I-AM-ENGINEER/AudMX/Images/photo_2024-06-28_22-19-17.jpg

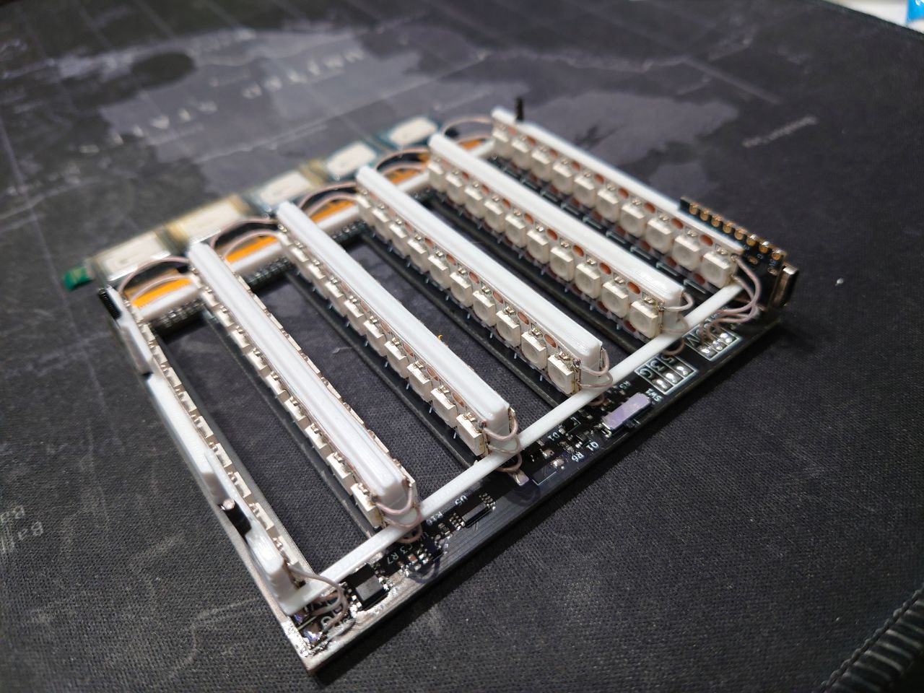
Images/photo_2024-06-28_22-19-17.jpg
