I-AM-ENGINEER/AudMX/AudMix/include/AudMX_logo.h

#pragma once

// 'A', 60x44px
const unsigned char epd_bitmap_A [] = {
	0x00, 0x00, 0x00, 0x7f, 0xe0, 0x00, 0x00, 0x00, 0x00, 0x00, 0x00, 0xff, 0xf0, 0x00, 0x00, 0x00, 
	0x00, 0x00, 0x00, 0xff, 0xf0, 0x00, 0x00, 0x00, 0x00, 0x00, 0x00, 0xff, 0xf0, 0x00, 0x00, 0x00, 
	0x00, 0x00, 0x01, 0xff, 0xf8, 0x00, 0x00, 0x00, 0x00, 0x00, 0x01, 0xff, 0xf8, 0x00, 0x00, 0x00, 
	0x00, 0x00, 0x03, 0xff, 0xf8, 0x00, 0x00, 0x00, 0x00, 0x00, 0x03, 0xff, 0xfc, 0x00, 0x00, 0x00, 
	0x00, 0x00, 0x03, 0xff, 0xfc, 0x00, 0x00, 0x00, 0x00, 0x00, 0x07, 0xff, 0xfc, 0x00, 0x00, 0x00, 
	0x00, 0x00, 0x07, 0xff, 0xfe, 0x00, 0x00, 0x00, 0x00, 0x00, 0x07, 0xfb, 0xfe, 0x00, 0x00, 0x00, 
	0x00, 0x00, 0x0f, 0xf9, 0xfe, 0x00, 0x00, 0x00, 0x00, 0x00, 0x0f, 0xf9, 0xff, 0x00, 0x00, 0x00, 
	0x00, 0x00, 0x0f, 0xf1, 0xff, 0x00, 0x00, 0x00, 0x00, 0x00, 0x1f, 0xf0, 0xff, 0x80, 0x00, 0x00, 
	0x00, 0x00, 0x1f, 0xf0, 0xff, 0x80, 0x00, 0x00, 0x00, 0x00, 0x1f, 0xe0, 0xff, 0x80, 0x00, 0x00, 
	0x00, 0x00, 0x3f, 0xe0, 0x7f, 0xc0, 0x00, 0x00, 0x00, 0x00, 0x3f, 0xe0, 0x7f, 0xc0, 0x00, 0x00, 
	0x00, 0x00, 0x7f, 0xc0, 0x7f, 0xc0, 0x00, 0x00, 0x00, 0x00, 0x7f, 0xc0, 0x3f, 0xe0, 0x00, 0x00, 
	0x00, 0x00, 0x7f, 0xc0, 0x3f, 0xe0, 0x00, 0x00, 0x00, 0x00, 0xff, 0x80, 0x3f, 0xe0, 0x00, 0x00, 
	0x00, 0x00, 0xff, 0x80, 0x3f, 0xf0, 0x00, 0x00, 0x00, 0x00, 0xff, 0x80, 0x1f, 0xf0, 0x00, 0x00, 
	0x00, 0x01, 0xff, 0xff, 0xff, 0xf8, 0x00, 0x00, 0x00, 0x01, 0xff, 0xff, 0xff, 0xf8, 0x00, 0x00, 
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
};

// Array of all bitmaps for convenience. (Total bytes used to store images in PROGMEM = 1840)
const unsigned char* AudMX_bitmap[5] = {
	epd_bitmap_A,
	epd_bitmap_u,
	epd_bitmap_d,
	epd_bitmap_M,
	epd_bitmap_X
};
