I-AM-ENGINEER/AudMX/AudMix/src/battery.cpp

#include "battery.hpp"
#include "freertos/FreeRTOS.h"
#include "freertos/task.h"
#include "stdio.h"
#include "esp_log.h"

#define EXAMPLE_ADC_UNIT                    ADC_UNIT_2
#define EXAMPLE_ADC_CONV_MODE               ADC_CONV_SINGLE_UNIT_2
#define EXAMPLE_ADC_ATTEN                   ADC_ATTEN_DB_11
#define EXAMPLE_ADC_BIT_WIDTH               SOC_ADC_DIGI_MAX_BITWIDTH

#define EXAMPLE_ADC_OUTPUT_TYPE             ADC_DIGI_OUTPUT_FORMAT_TYPE2
#define EXAMPLE_ADC_GET_CHANNEL(p_data)     ((p_data)->type2.channel)
#define EXAMPLE_ADC_GET_DATA(p_data)        ((p_data)->type2.data)

#define EXAMPLE_READ_LEN                    4

static adc_channel_t channel[1] = {ADC_CHANNEL_0};

const static char *TAG = "BATTERY";

static TaskHandle_t s_task_handle;

adc_continuous_handle_t     _adc_handle;

static bool IRAM_ATTR s_conv_done_cb(adc_continuous_handle_t handle, const adc_continuous_evt_data_t *edata, void *user_data){
    BaseType_t mustYield = pdFALSE;
    //Notify that ADC continuous driver has done enough number of conversions
    vTaskNotifyGiveFromISR(s_task_handle, &mustYield);

    return (mustYield == pdTRUE);
}

static volatile int32_t adc_val;

static bool example_adc_calibration_init(adc_unit_t unit, adc_channel_t channel, adc_atten_t atten, adc_cali_handle_t *out_handle);

void BatteryTask( void* args ){
    
    uint8_t result[EXAMPLE_READ_LEN] = {0};
    //memset(result, 0xcc, EXAMPLE_READ_LEN);
    uint32_t ret_num = 0;
    while (1){
        
        adc_continuous_start(_adc_handle);
        ulTaskNotifyTake(pdTRUE, pdMS_TO_TICKS(100));
        //printf("Hey!\r\n");
        adc_continuous_read(_adc_handle, result, EXAMPLE_READ_LEN, &ret_num, 0);
        
        for (int i = 0; i < ret_num; i += SOC_ADC_DIGI_RESULT_BYTES) {
            adc_digi_output_data_t *p = (adc_digi_output_data_t*)&result[i];
            adc_val = EXAMPLE_ADC_GET_DATA(p);
        }
        vTaskDelay(100);
    }
}

void Battery::init( void ){
    adc_continuous_handle_t handle = NULL;

    adc_continuous_handle_cfg_t adc_config = {
        .max_store_buf_size = 1024,
        .conv_frame_size = EXAMPLE_READ_LEN,
    };
    ESP_ERROR_CHECK(adc_continuous_new_handle(&adc_config, &handle));

    adc_continuous_config_t dig_cfg = {
        .sample_freq_hz = 20 * 1000,
        .conv_mode = EXAMPLE_ADC_CONV_MODE,
        .format = EXAMPLE_ADC_OUTPUT_TYPE,
    };

    adc_digi_pattern_config_t adc_pattern[SOC_ADC_PATT_LEN_MAX] = {0};
    dig_cfg.pattern_num = 1;
    for (int i = 0; i < 1; i++) {
        adc_pattern[i].atten = EXAMPLE_ADC_ATTEN;
        adc_pattern[i].channel = channel[i] & 0x7;
        adc_pattern[i].unit = EXAMPLE_ADC_UNIT;
        adc_pattern[i].bit_width = EXAMPLE_ADC_BIT_WIDTH;
    }
    dig_cfg.adc_pattern = adc_pattern;
    ESP_ERROR_CHECK(adc_continuous_config(handle, &dig_cfg));

    adc_continuous_evt_cbs_t cbs = {
        .on_conv_done = s_conv_done_cb,
    };

    example_adc_calibration_init(EXAMPLE_ADC_UNIT, ADC_CHANNEL_0, EXAMPLE_ADC_ATTEN, &_adc_cali);

    ESP_ERROR_CHECK(adc_continuous_register_event_callbacks(handle, &cbs, NULL));
    
    xTaskCreate(BatteryTask, "batteryTask", 2000, NULL, 1, &s_task_handle);
    //ESP_ERROR_CHECK(adc_continuous_start(handle));

    
    _adc_handle = handle;
}

/// @brief Read battery voltage
/// @param  
/// @return mv
uint16_t Battery::readVoltage( void ){
    int mV;
    adc_cali_raw_to_voltage(_adc_cali, adc_val, &mV);
    return mV;
}

/// @brief Read battery level 0.0...1.0
/// @param  
/// @return 0.0 - fully discharged, 1.0 - fully charged
float Battery::readLevel( void ){
    float adc_mv = (float)readVoltage();
    float battery_mv = adc_mv * 2.0f;
    float battery_charge =  (battery_mv - 3400.0f) / 700.0f;
    if(battery_charge < 0.0f){
        battery_charge = 0.0f;
    }else if(battery_charge > 1.0f){
        battery_charge = 1.0f;
    }
    return battery_charge;
}


/*---------------------------------------------------------------
        ADC Calibration
---------------------------------------------------------------*/
static bool example_adc_calibration_init(adc_unit_t unit, adc_channel_t channel, adc_atten_t atten, adc_cali_handle_t *out_handle)
{
    adc_cali_handle_t handle = NULL;
    esp_err_t ret = ESP_FAIL;
    bool calibrated = false;

#if ADC_CALI_SCHEME_CURVE_FITTING_SUPPORTED
    if (!calibrated) {
        ESP_LOGI(TAG, "calibration scheme version is %s", "Curve Fitting");
        adc_cali_curve_fitting_config_t cali_config = {
            .unit_id = unit,
            .chan = channel,
            .atten = atten,
            .bitwidth = ADC_BITWIDTH_DEFAULT,
        };
        ret = adc_cali_create_scheme_curve_fitting(&cali_config, &handle);
        if (ret == ESP_OK) {
            calibrated = true;
        }
    }
#endif

#if ADC_CALI_SCHEME_LINE_FITTING_SUPPORTED
    if (!calibrated) {
        ESP_LOGI(TAG, "calibration scheme version is %s", "Line Fitting");
        adc_cali_line_fitting_config_t cali_config = {
            .unit_id = unit,
            .atten = atten,
            .bitwidth = ADC_BITWIDTH_DEFAULT,
        };
        ret = adc_cali_create_scheme_line_fitting(&cali_config, &handle);
        if (ret == ESP_OK) {
            calibrated = true;
        }
    }
#endif

    *out_handle = handle;
    if (ret == ESP_OK) {
        ESP_LOGI(TAG, "Calibration Success");
    } else if (ret == ESP_ERR_NOT_SUPPORTED || !calibrated) {
        ESP_LOGW(TAG, "eFuse not burnt, skip software calibration");
    } else {
        ESP_LOGE(TAG, "Invalid arg or no memory");
    }

    return calibrated;
}

static void example_adc_calibration_deinit(adc_cali_handle_t handle)
{
#if ADC_CALI_SCHEME_CURVE_FITTING_SUPPORTED
    ESP_LOGI(TAG, "deregister %s calibration scheme", "Curve Fitting");
    ESP_ERROR_CHECK(adc_cali_delete_scheme_curve_fitting(handle));

#elif ADC_CALI_SCHEME_LINE_FITTING_SUPPORTED
    ESP_LOGI(TAG, "deregister %s calibration scheme", "Line Fitting");
    ESP_ERROR_CHECK(adc_cali_delete_scheme_line_fitting(handle));
#endif
}
